indraAsLesmana/dl380-case/docs/02A_rail_final_upgrade.png

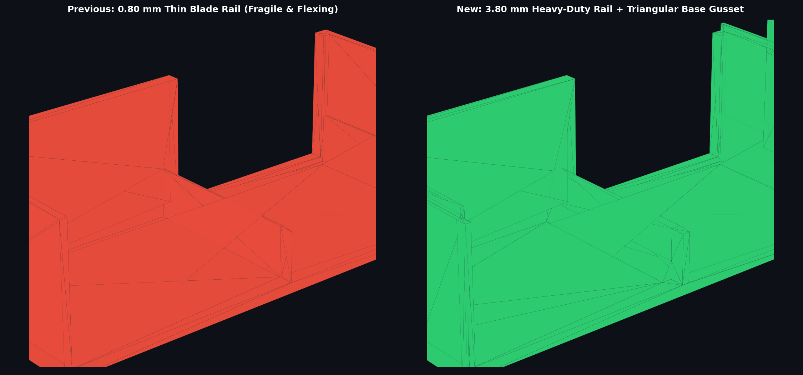
docs/02A_rail_final_upgrade.png
