indraAsLesmana/dl380-case/docs/02A_rail_thickness_comparison.png

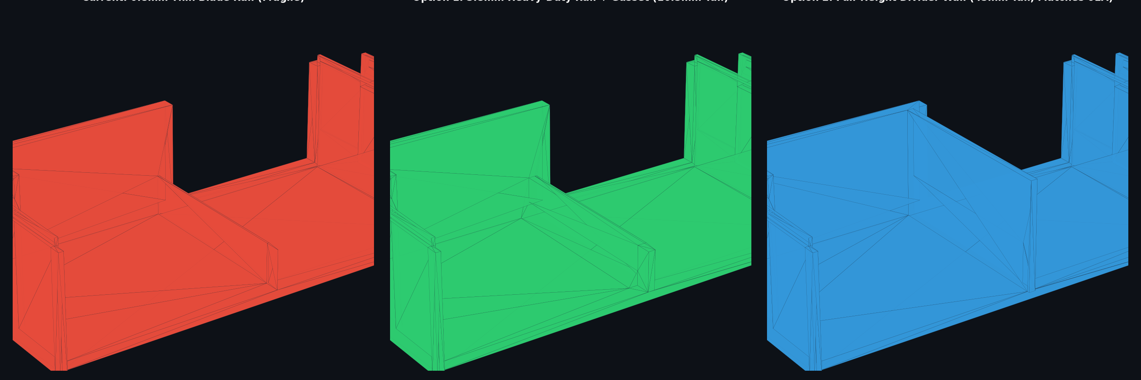
docs/02A_rail_thickness_comparison.png
