indraAsLesmana/dl380-case/docs/02A_rotation_warning.png

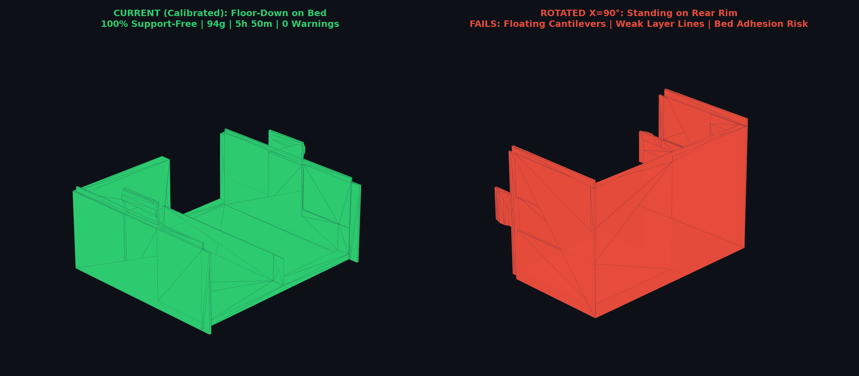
docs/02A_rotation_warning.png
