indraAsLesmana/dl380-case/docs/02A_snap_comparison.png

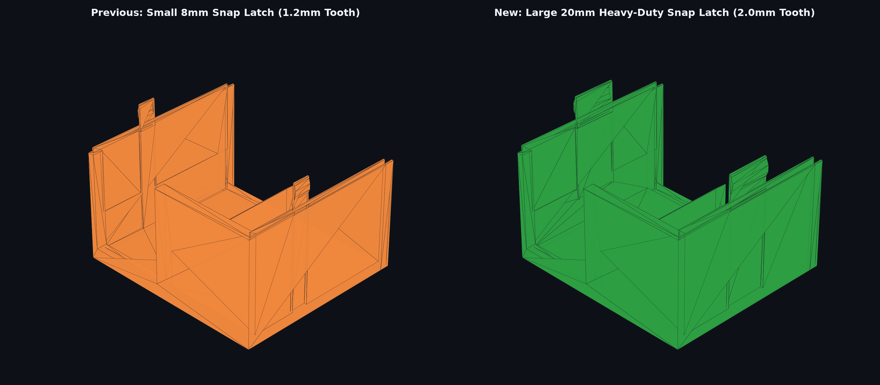
docs/02A_snap_comparison.png
