indraAsLesmana/dl380-case/docs/02A_snap_layer_diagram.png

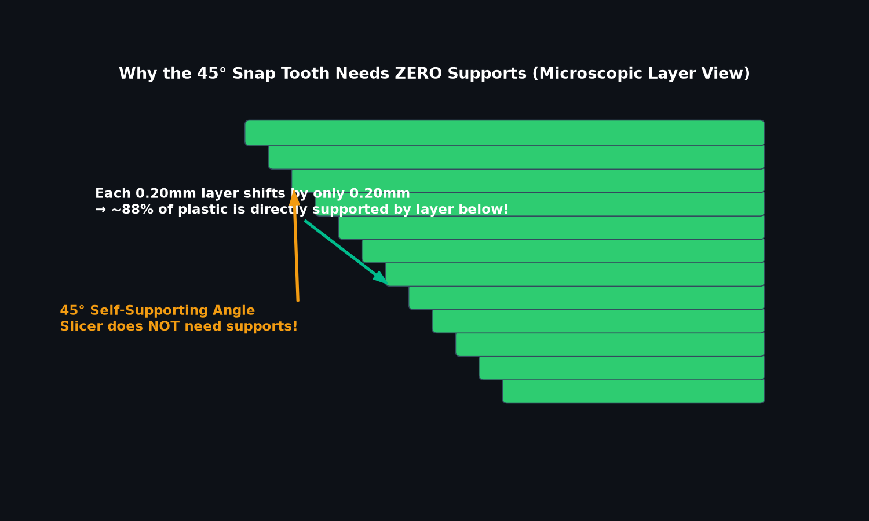
docs/02A_snap_layer_diagram.png
