indraAsLesmana/dl380-case/docs/02B_fan_grille_detail.png

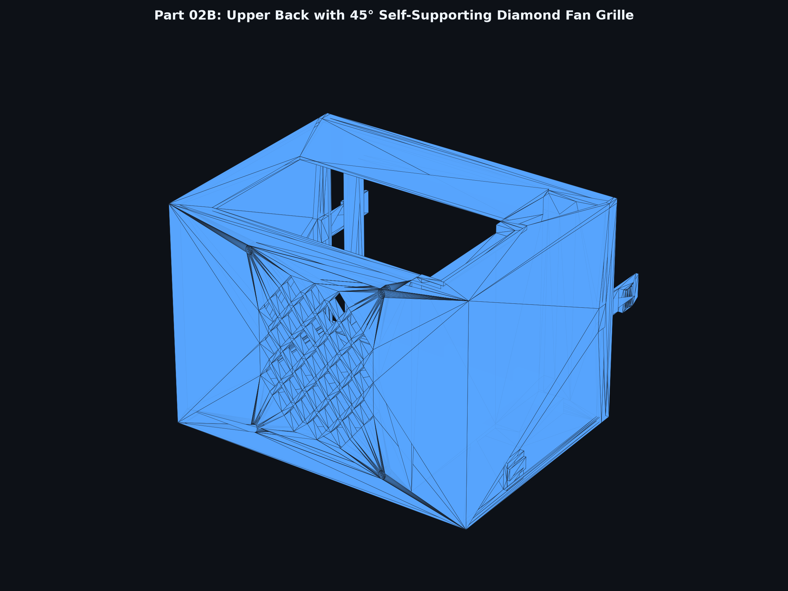
docs/02B_fan_grille_detail.png
