indraAsLesmana/dl380-case/docs/02B_thick_side_analysis.png

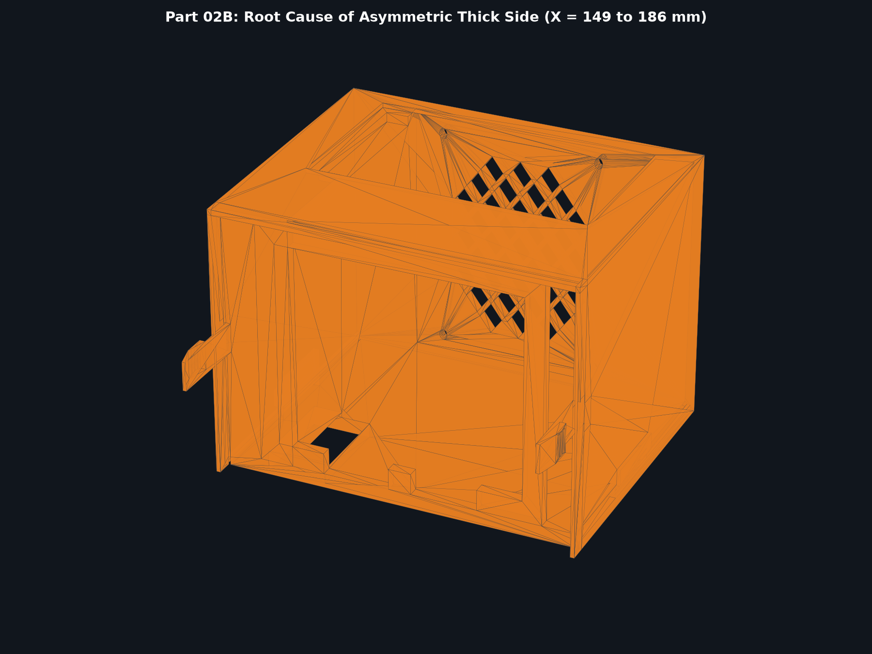
docs/02B_thick_side_analysis.png
