indraAsLesmana/dl380-case/docs/cage_retention_pin_diagram.png

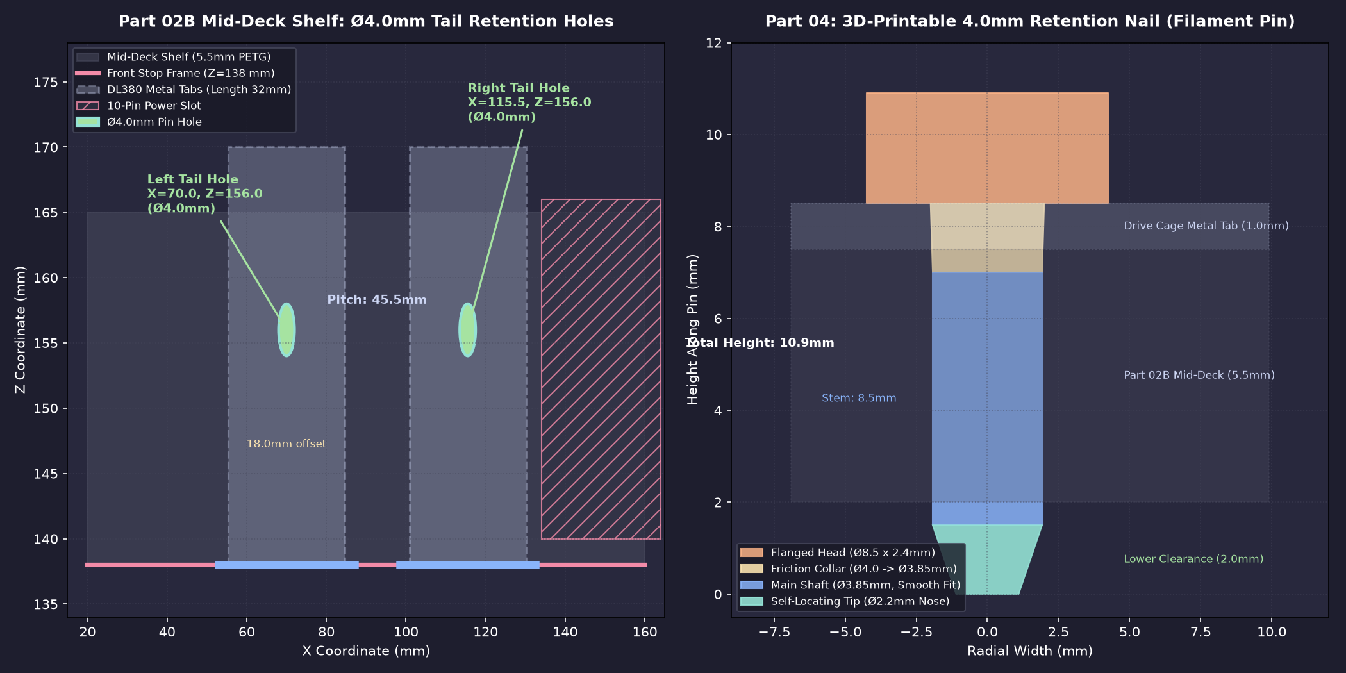
docs/cage_retention_pin_diagram.png
