indraAsLesmana/dl380-case/docs/digital_capler/10-pin-backplane-width.jpeg

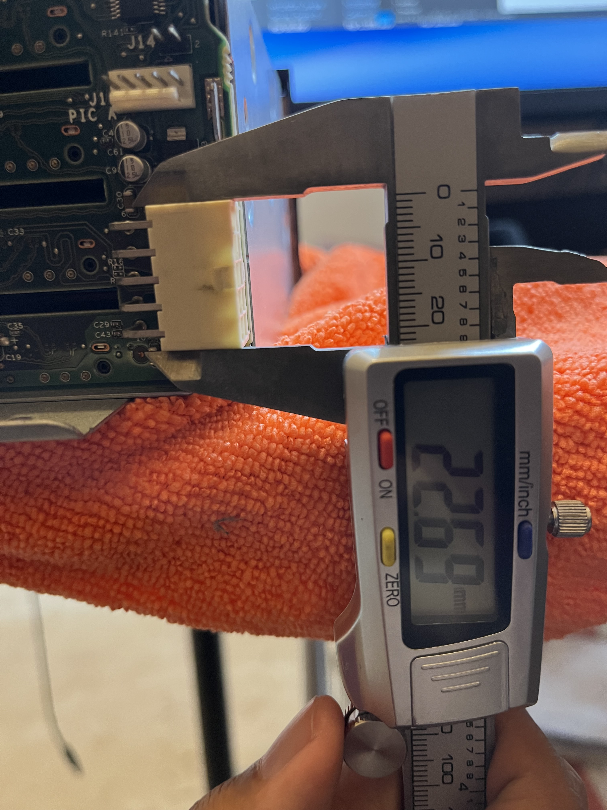
docs/digital_capler/10-pin-backplane-width.jpeg
