indraAsLesmana/dl380-case/docs/digital_capler/10-pin-to-top-backplane.jpeg

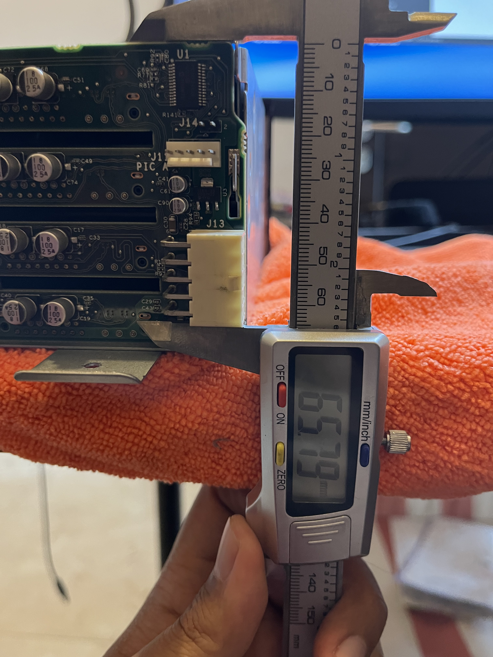
docs/digital_capler/10-pin-to-top-backplane.jpeg
