indraAsLesmana/dl380-case/docs/digital_capler/backplane_tail_height.jpeg

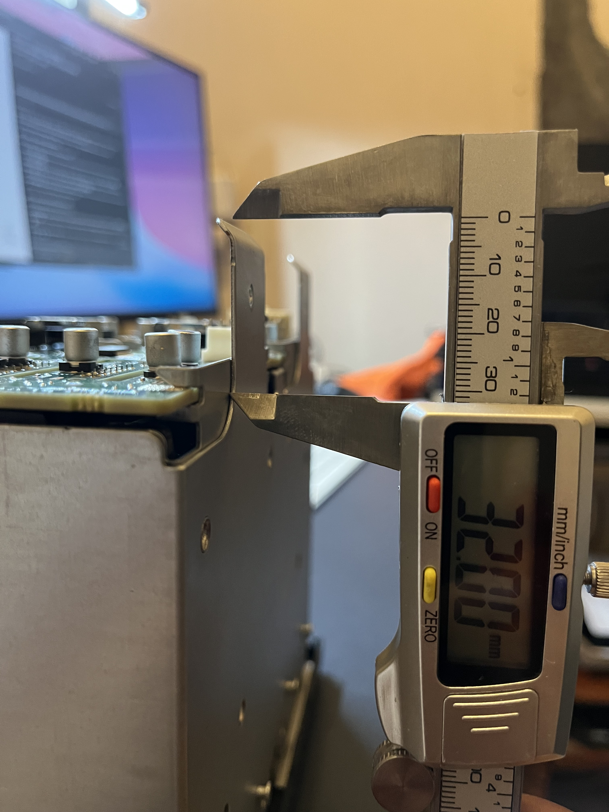
docs/digital_capler/backplane_tail_height.jpeg
