indraAsLesmana/dl380-case/docs/digital_capler/backplane_tail_width.jpeg

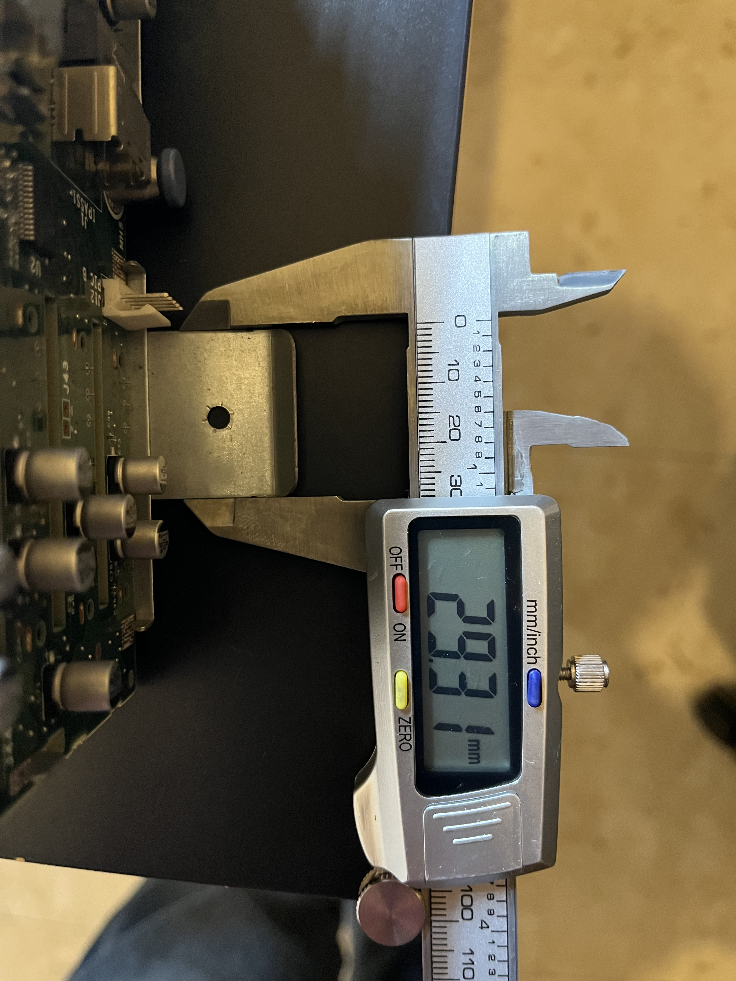
docs/digital_capler/backplane_tail_width.jpeg
