indraAsLesmana/dl380-case/docs/digital_capler/disc_cage_metal_height.jpeg

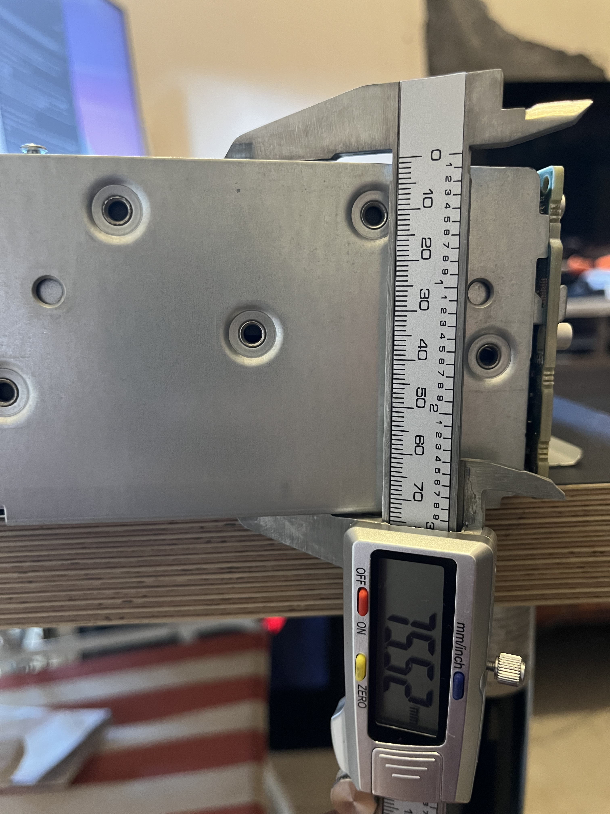
docs/digital_capler/disc_cage_metal_height.jpeg
