indraAsLesmana/dl380-case/docs/digital_capler/front_plastic_case_thick.jpeg

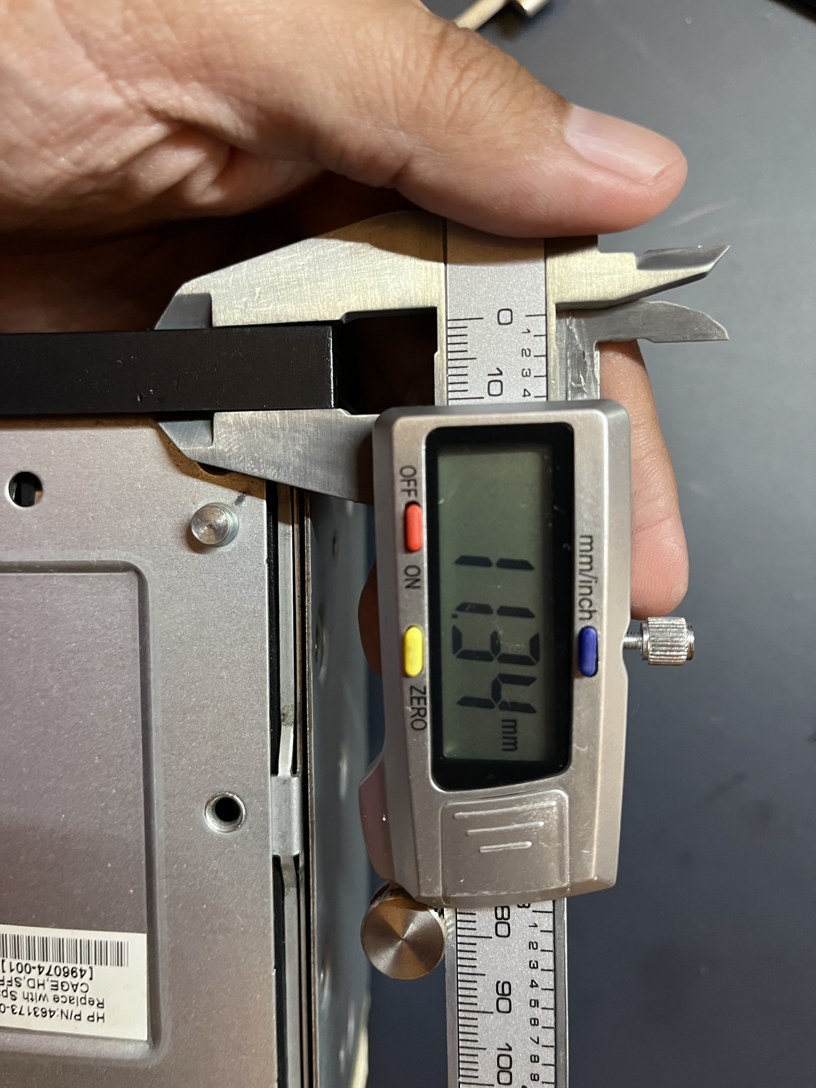
docs/digital_capler/front_plastic_case_thick.jpeg
