indraAsLesmana/dl380-case/docs/digital_capler/front_plastic_height.jpeg

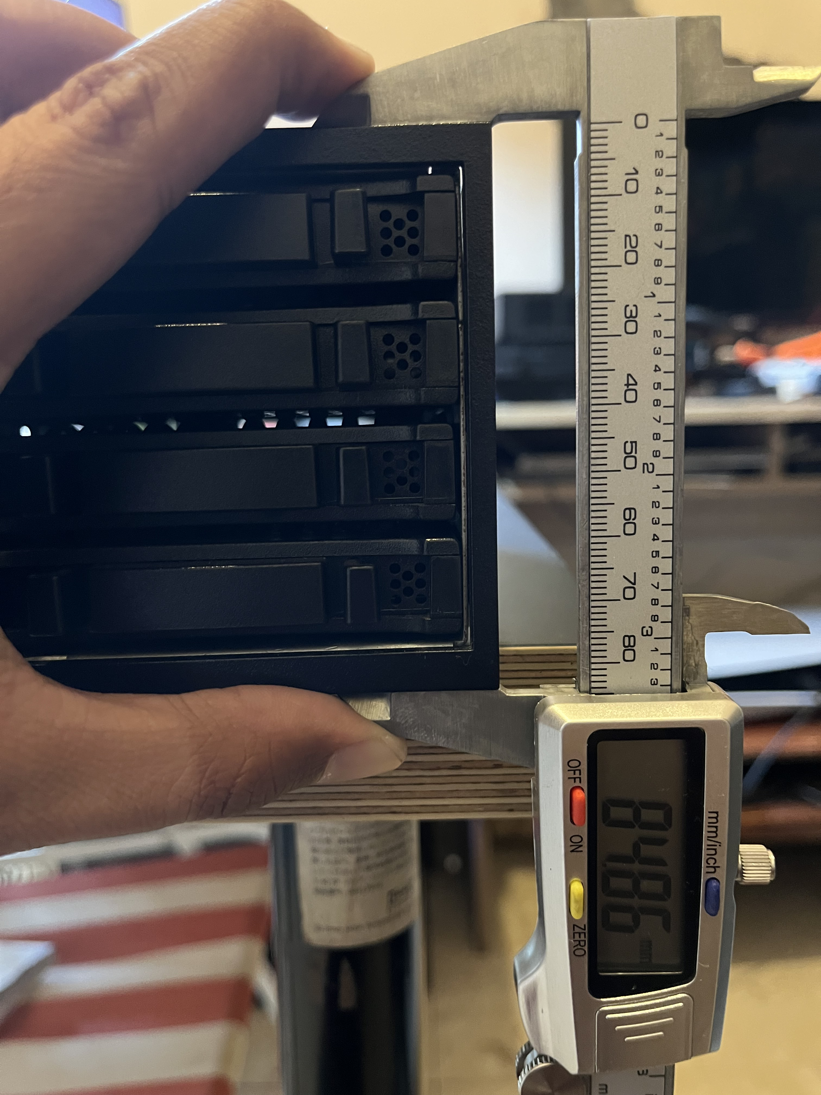
docs/digital_capler/front_plastic_height.jpeg
