indraAsLesmana/dl380-case/docs/digital_capler/top_disccage_to_plastic_front_bottom-height.jpeg

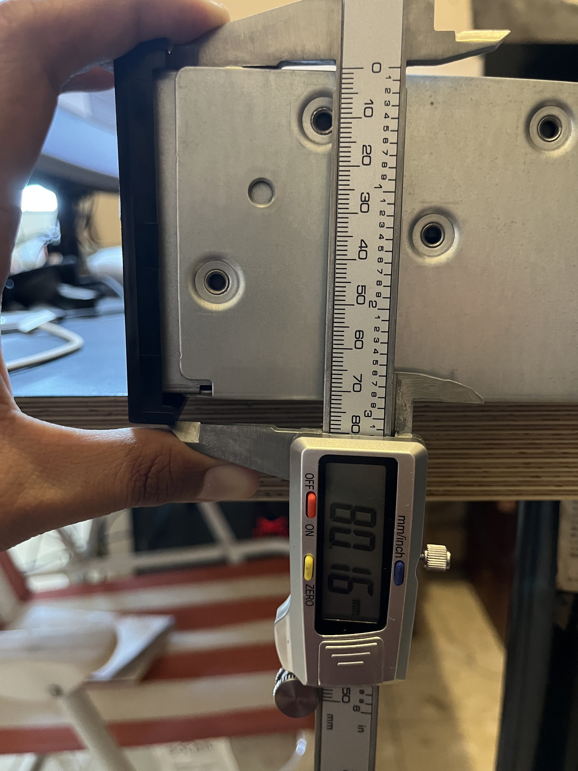
docs/digital_capler/top_disccage_to_plastic_front_bottom-height.jpeg
