indraAsLesmana/dl380-case/docs/dl380_flex_case_views.png

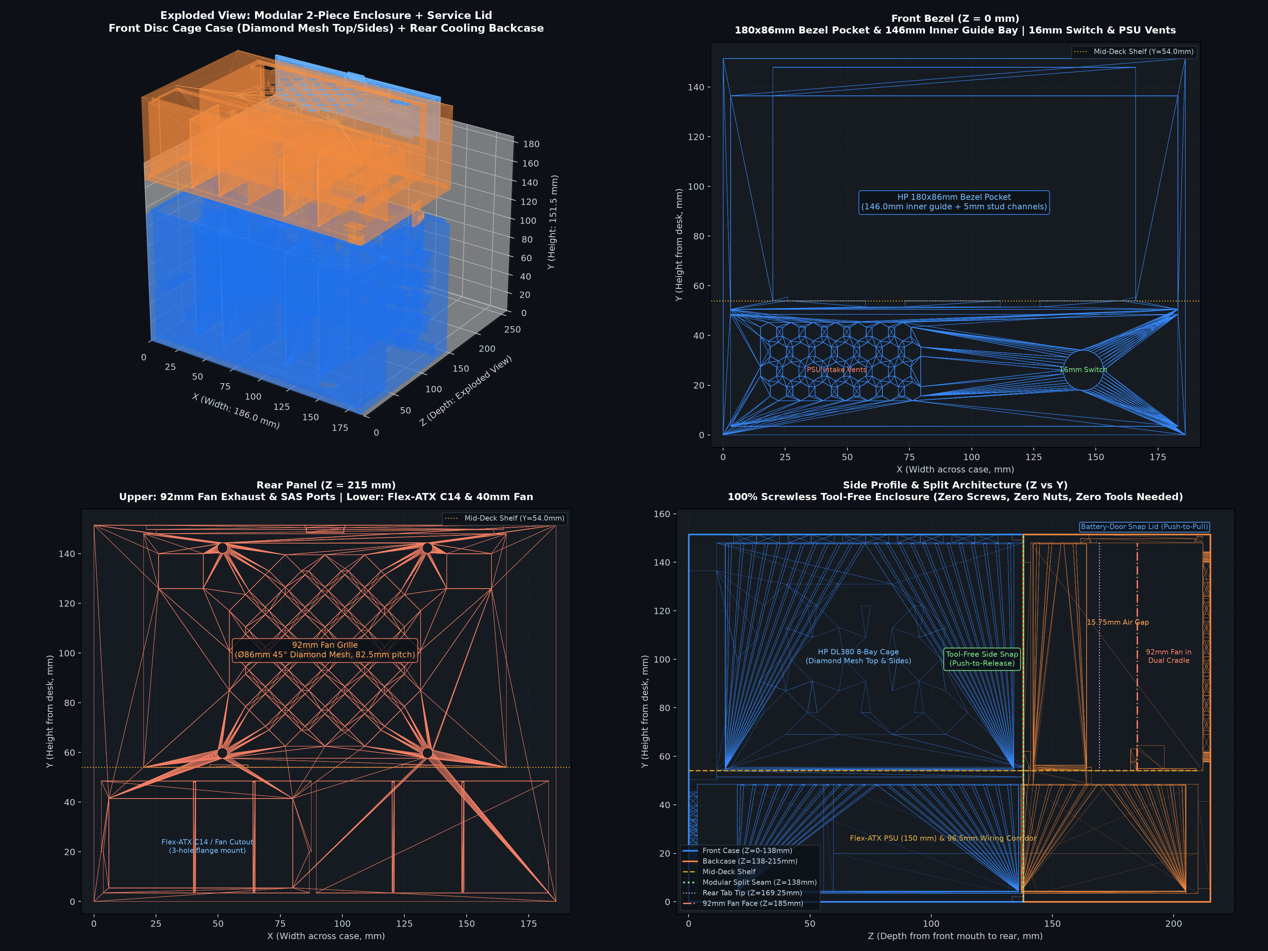
docs/dl380_flex_case_views.png
