indraAsLesmana/dl380-case/docs/fan_grille_comparison.png

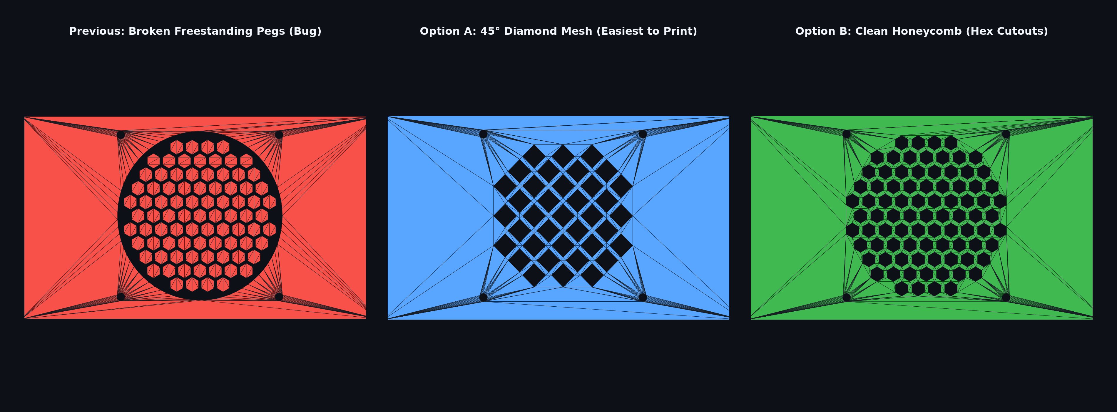
docs/fan_grille_comparison.png
