indraAsLesmana/dl380-case/docs/orientation_analysis_comparison.png

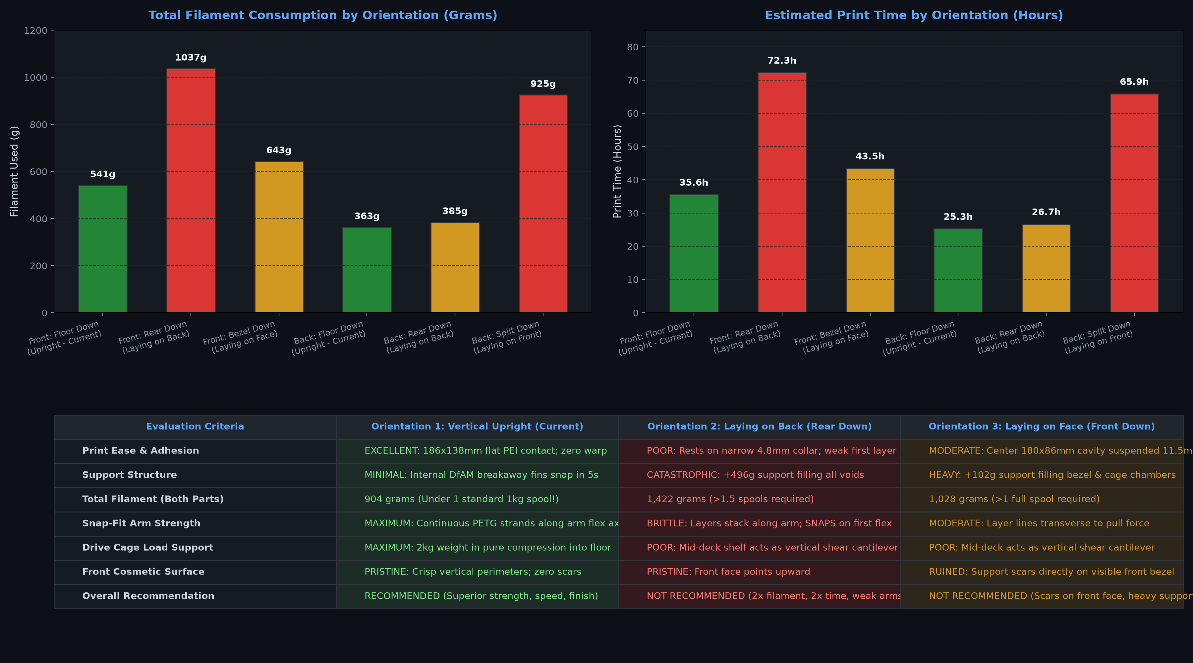
docs/orientation_analysis_comparison.png
