indraAsLesmana/dl380-case/docs/psu_tool_free_retention.png

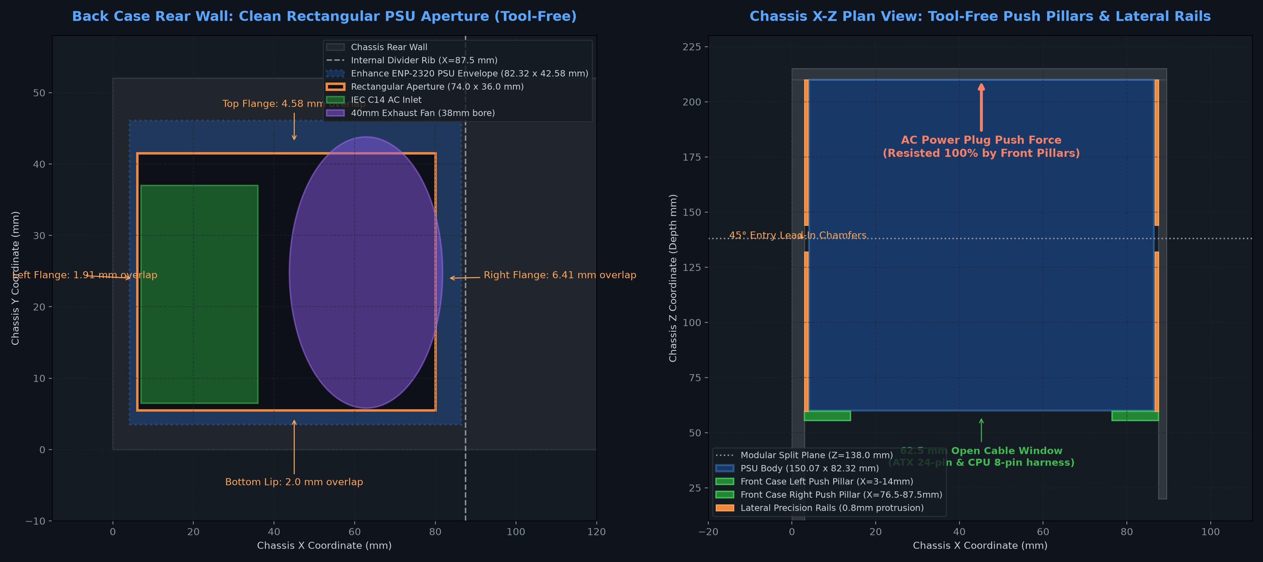
docs/psu_tool_free_retention.png
