indraAsLesmana/dl380-case/docs/reference/cage-rear-upright-cable.png

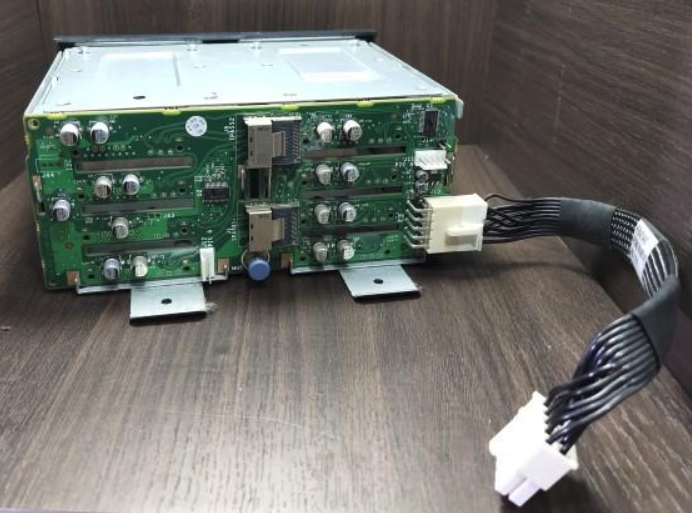
docs/reference/cage-rear-upright-cable.png
