indraAsLesmana/dl380-case/docs/reference/psu-dimension/IMG_1393.jpeg

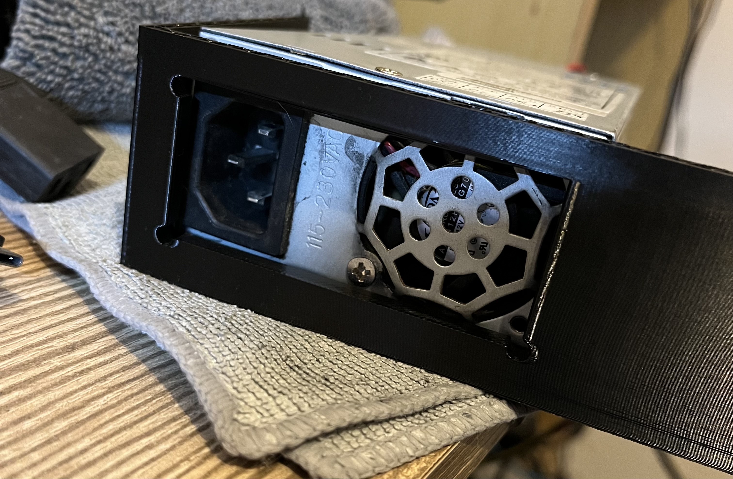
docs/reference/psu-dimension/IMG_1393.jpeg
