indraAsLesmana/dl380-case/docs/reference/s-l1600 front.webp

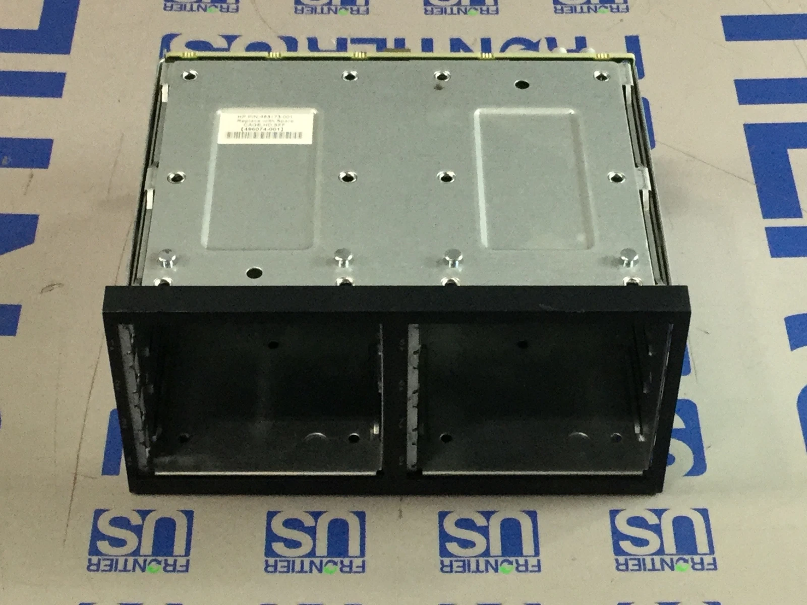
docs/reference/s-l1600 front.webp
