indraAsLesmana/dl380-case/out/body_side.png

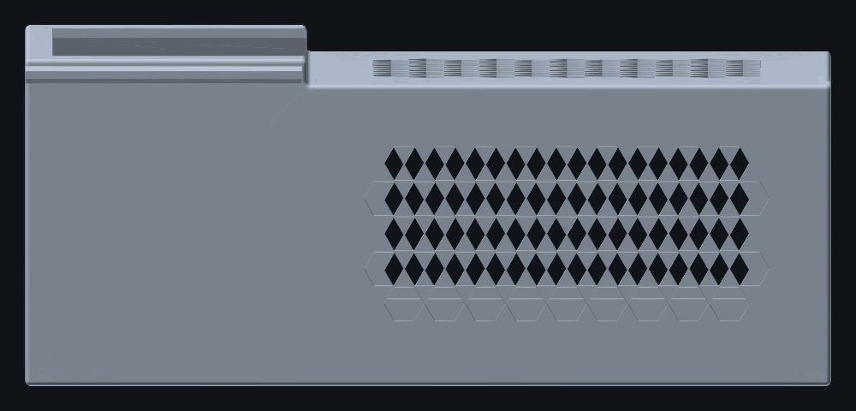
out/body_side.png
