indraAsLesmana/dl380-case/out/body_top.png

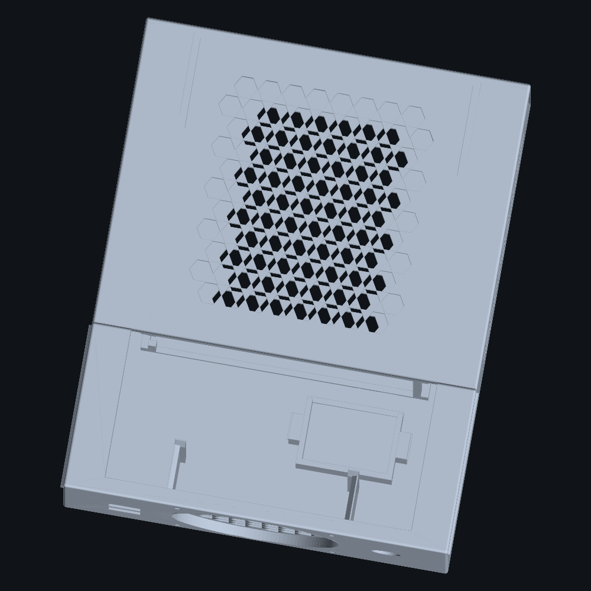
out/body_top.png
