indraAsLesmana/dl380-case/out/lid_cut.png

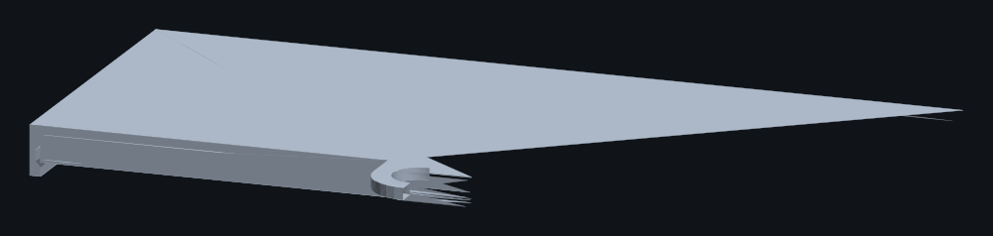
out/lid_cut.png
