indraAsLesmana/dl380-case/out/lid_front.png

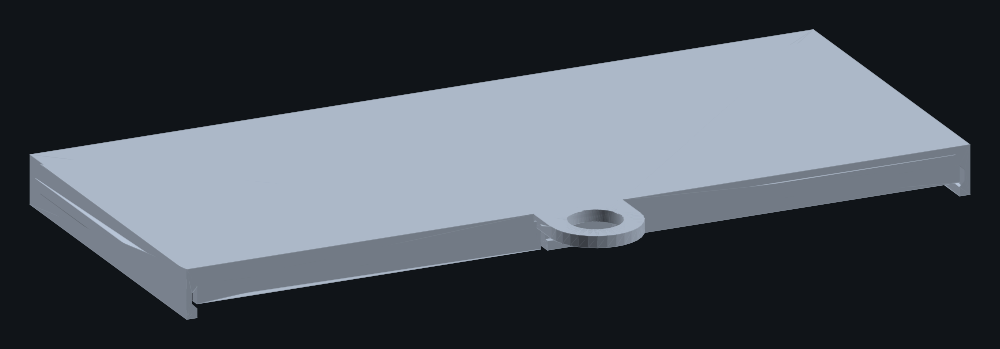
out/lid_front.png
