indraAsLesmana/dl380-case/out/lid_rear.png

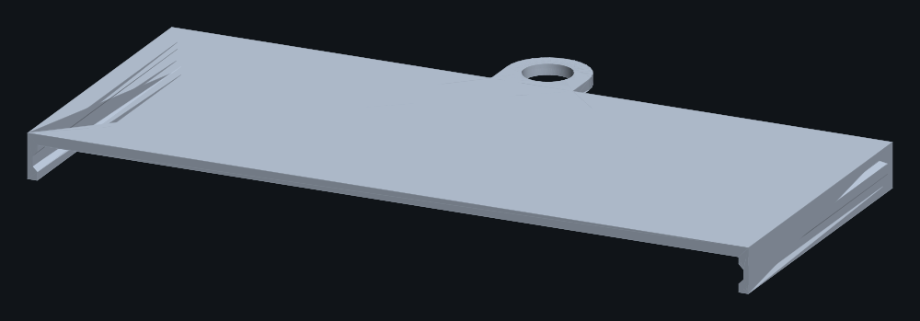
out/lid_rear.png
