indraAsLesmana/dl380-case/out/lid_side.png

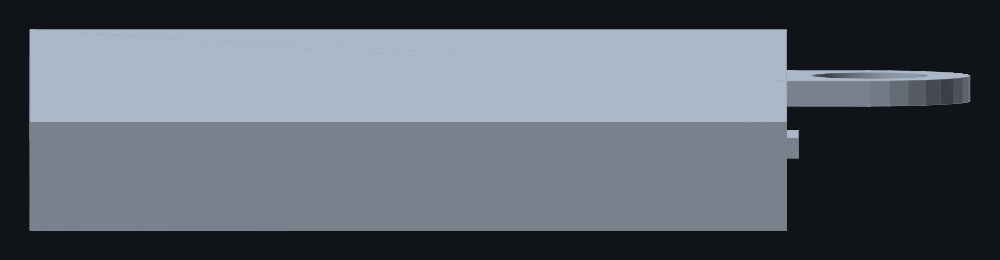
out/lid_side.png
