indraAsLesmana/dl380-case/out/lid_top.png

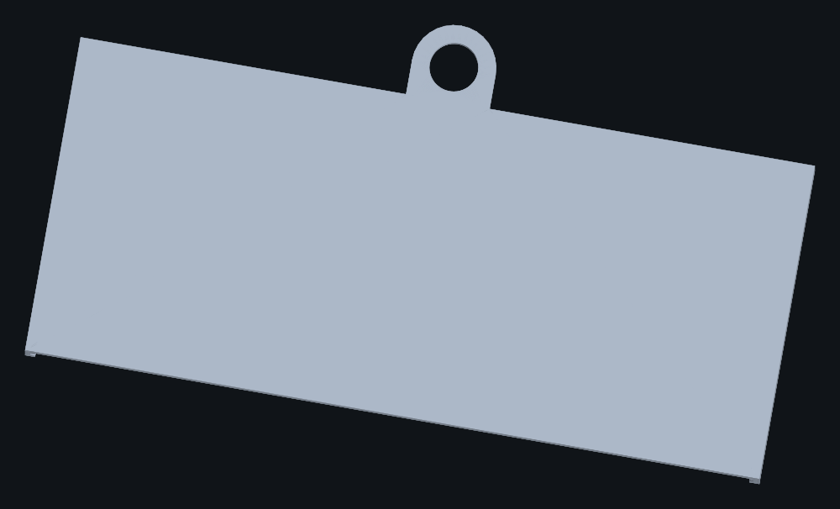
out/lid_top.png
