indraAsLesmana/dl380-case/out/strap_cut.png

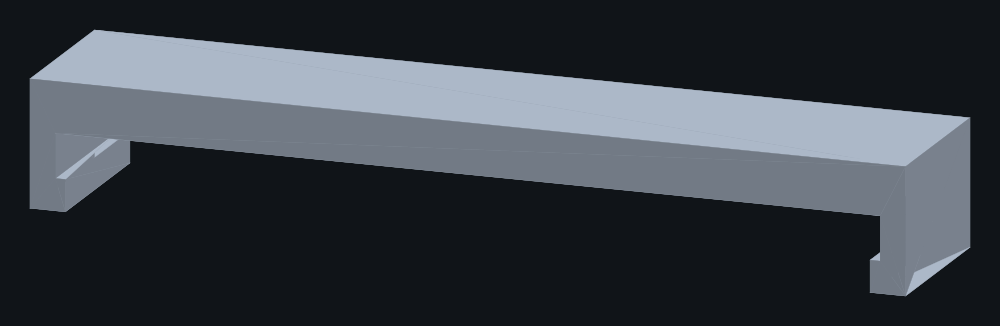
out/strap_cut.png
