indraAsLesmana/dl380-case/out/strap_front.png

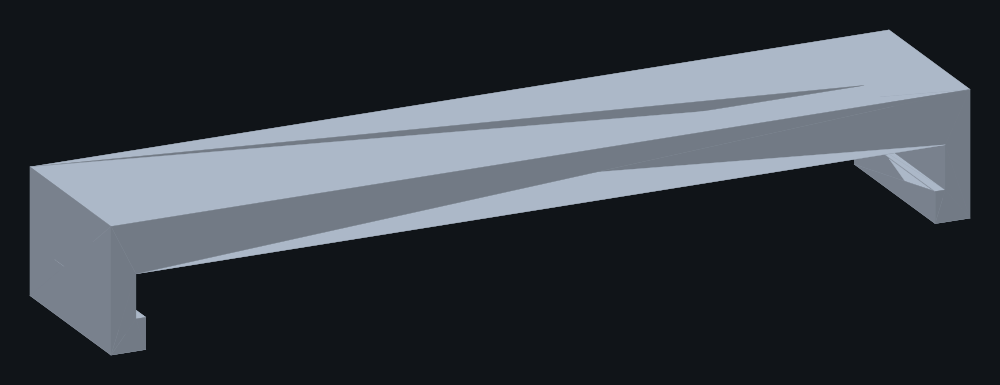
out/strap_front.png
