indraAsLesmana/dl380-case/out/strap_top.png

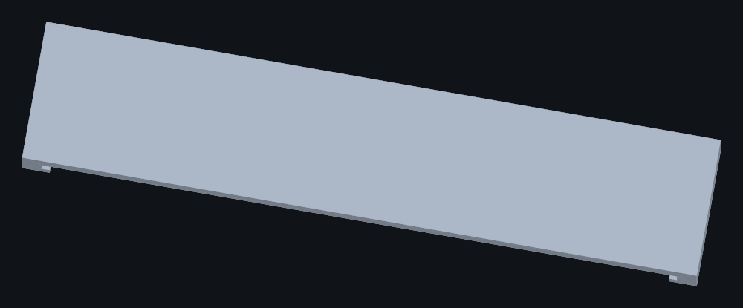
out/strap_top.png
