indraAsLesmana/dl380-case/print/dl380_back_case.stl

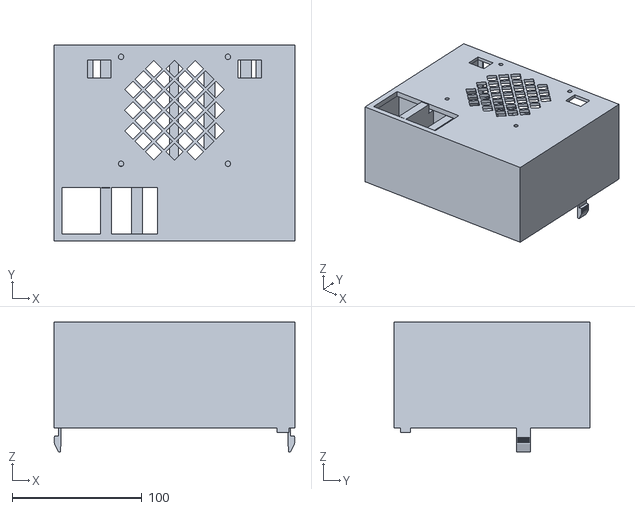
[picture p64: CAD file, 2026-10-03]
print/dl380_back_case.stl
186.0 x 151.5 x 100.0
