indraAsLesmana/dl380-case/out/4piece/01B_upper_front.step

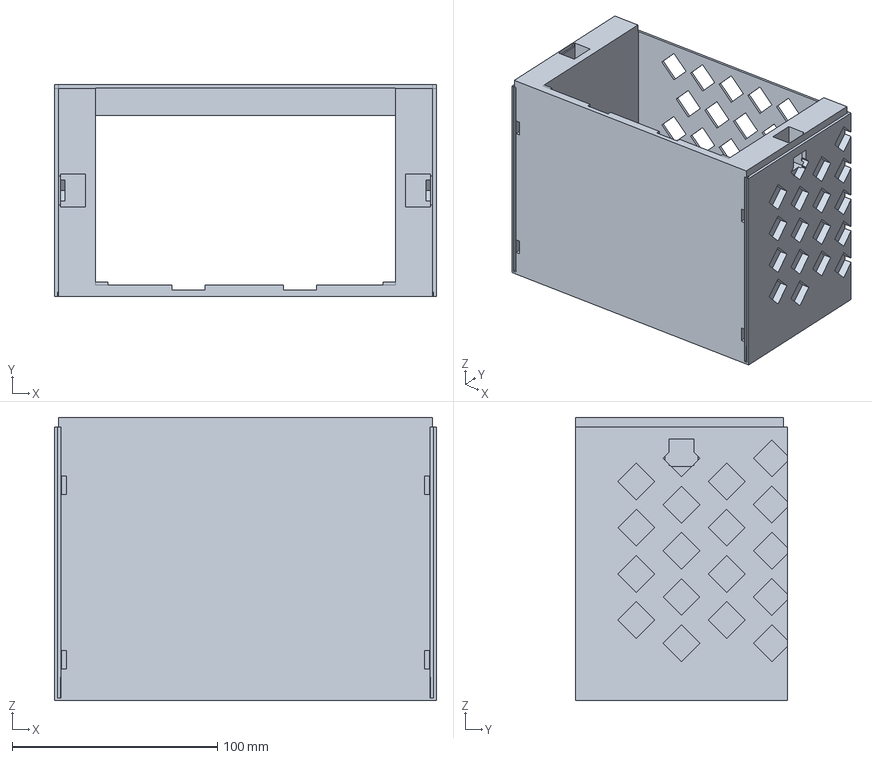
[picture p65: CAD file, 2026-10-03]
out/4piece/01B_upper_front.step
186.0 x 103.0 x 138.0 mm
