indraAsLesmana/dl380-case/out/4piece/04_drive_cage_pin.step

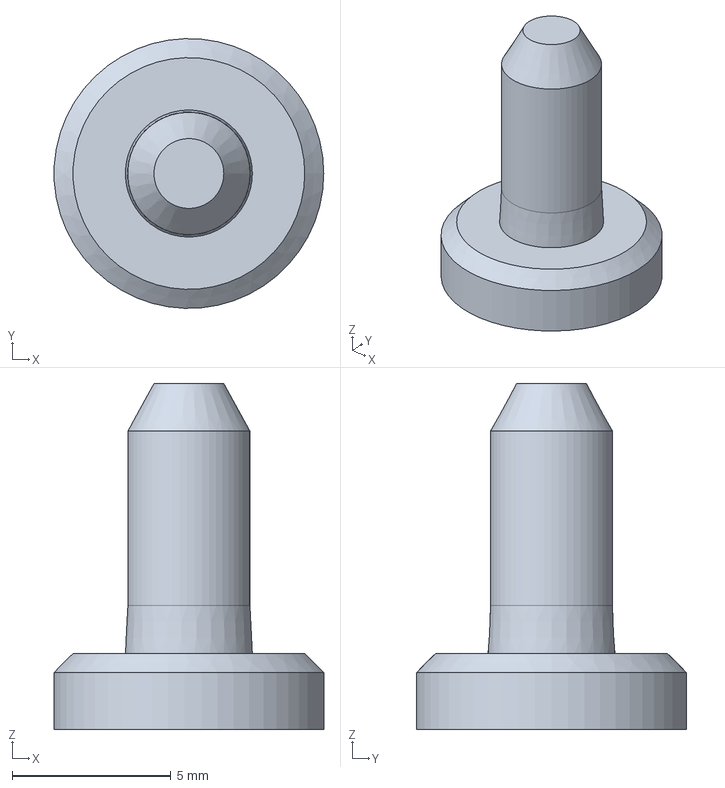
[picture p66: CAD file, 2026-10-03]
out/4piece/04_drive_cage_pin.step
8.49 x 8.50 x 10.9 mm
