indraAsLesmana/dl380-case/print_service_package/4piece/03_dl380_service_lid.3mf

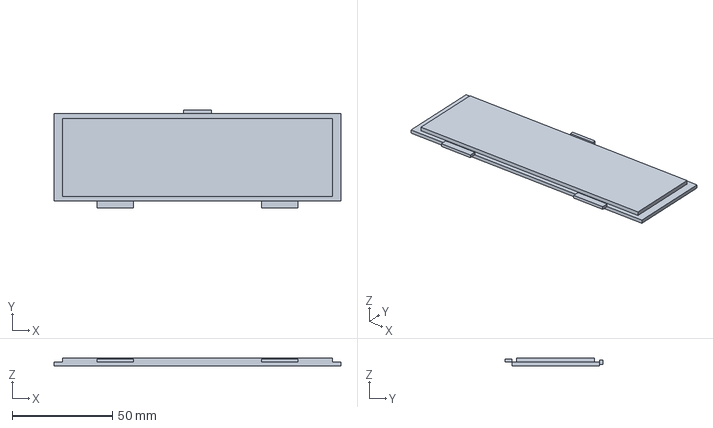
[picture p67: CAD file, 2026-10-03]
print_service_package/4piece/03_dl380_service_lid.3mf
143.0 x 49.0 x 3.80 mm
