indraAsLesmana/dl380-case/out/dl380_flex_case.step

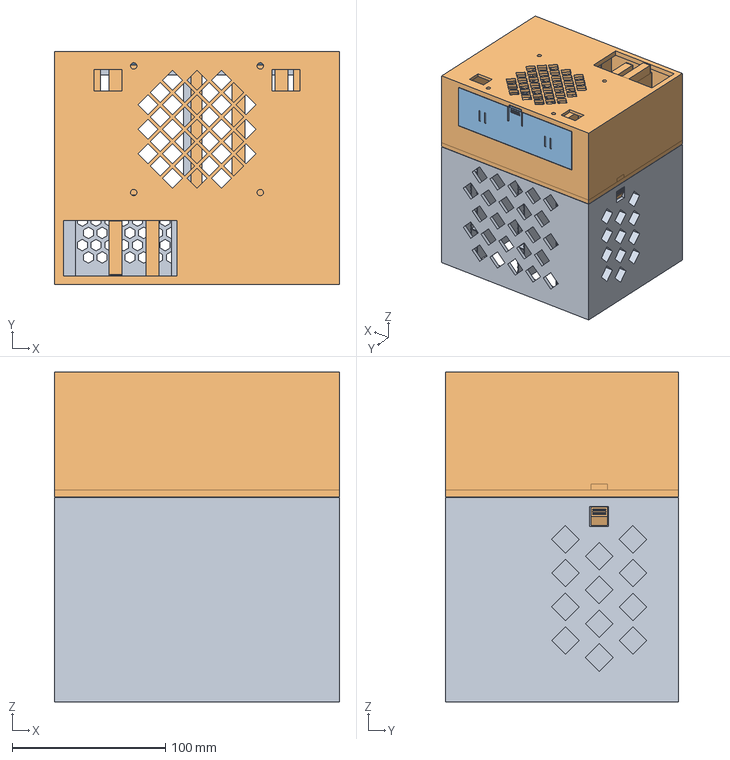
[picture p68: CAD file, 2026-10-03]
out/dl380_flex_case.step
186.0 x 151.5 x 215.0 mm
