indraAsLesmana/dl380-case/print/dl380_flex_case_all-parts.stl

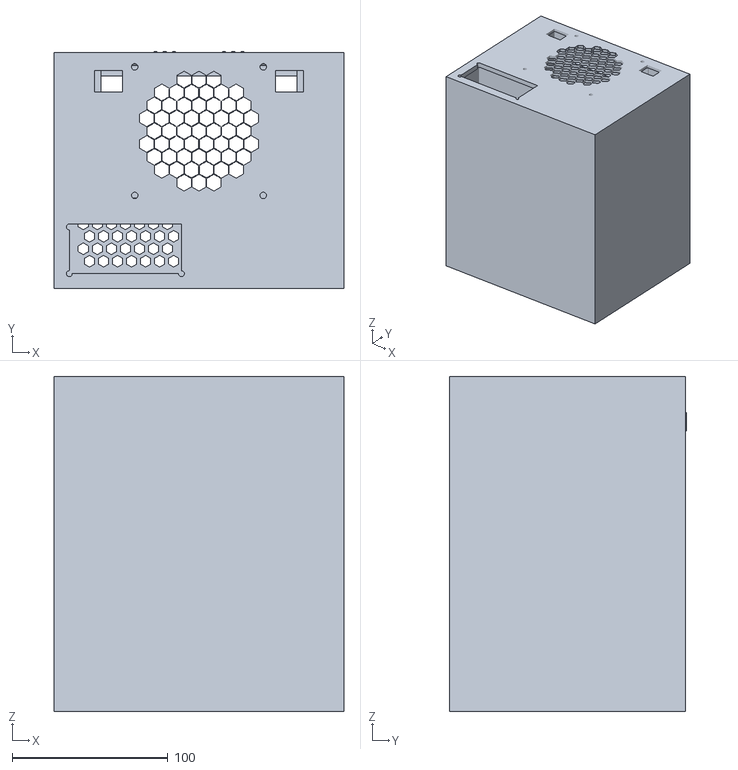
[picture p69: CAD file, 2026-09-29]
print/dl380_flex_case_all-parts.stl
186.0 x 152.1 x 215.0
