indraAsLesmana/dl380-case/print/dl380-case_psu-strap.stl

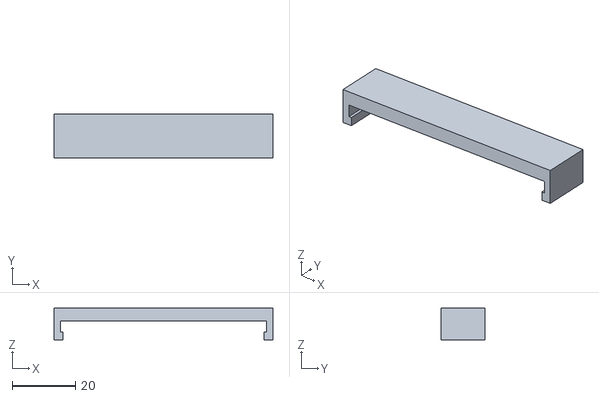
[picture p70: CAD file, 2026-09-24]
print/dl380-case_psu-strap.stl
69.2 x 14.0 x 10.0
