indraAsLesmana/dl380-case/out/dl380_flex_case_lid.step

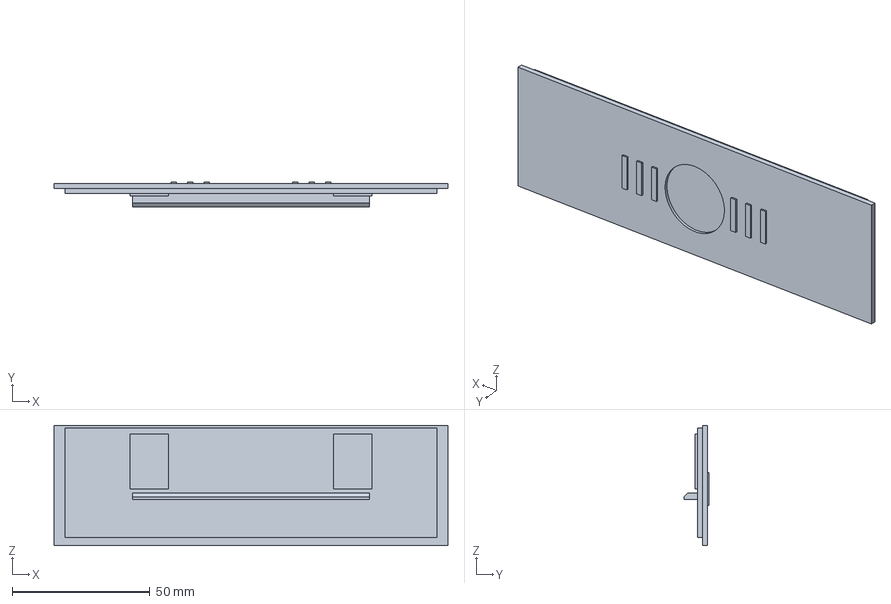
[picture p71: CAD file, 2026-09-29]
out/dl380_flex_case_lid.step
143.0 x 9.10 x 43.7 mm
