indraAsLesmana/dl380-case/print/dl380-case_body.stl

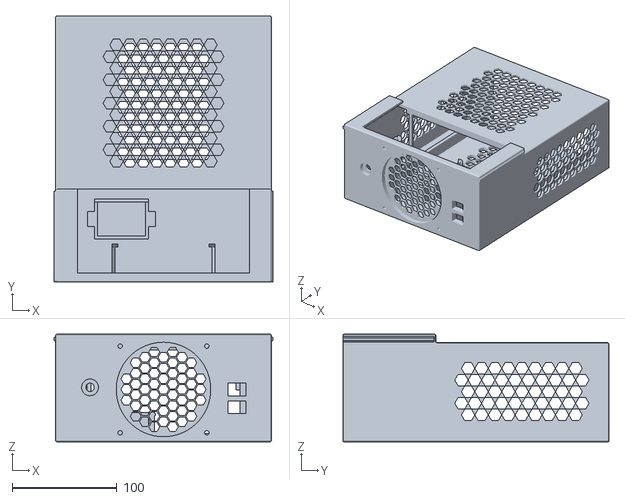
[picture p72: CAD file, 2026-09-24]
print/dl380-case_body.stl
208.4 x 253.4 x 102.8
