indraAsLesmana/dl380-case/print_service_package/4piece/04_dl380_cage_pins.3mf

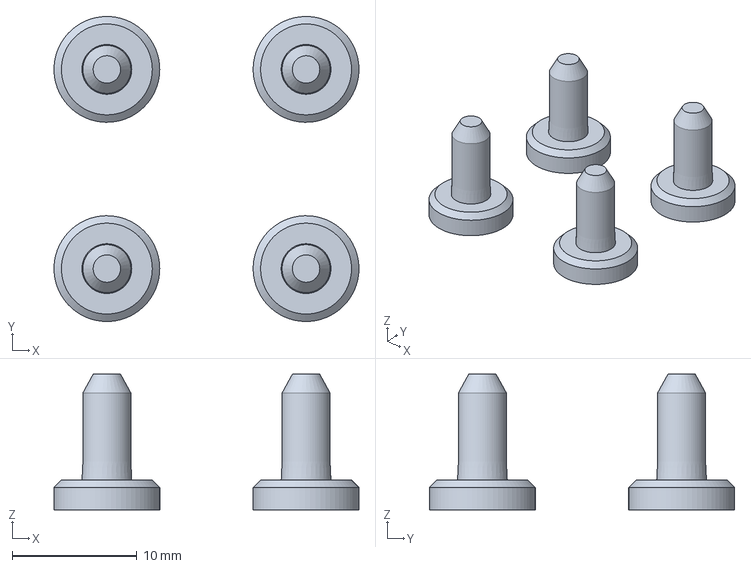
[picture p73: CAD file, 2026-10-03]
print_service_package/4piece/04_dl380_cage_pins.3mf
24.5 x 24.5 x 10.9 mm
