indraAsLesmana/dl380-case/out/dl380_flex_case_body.step

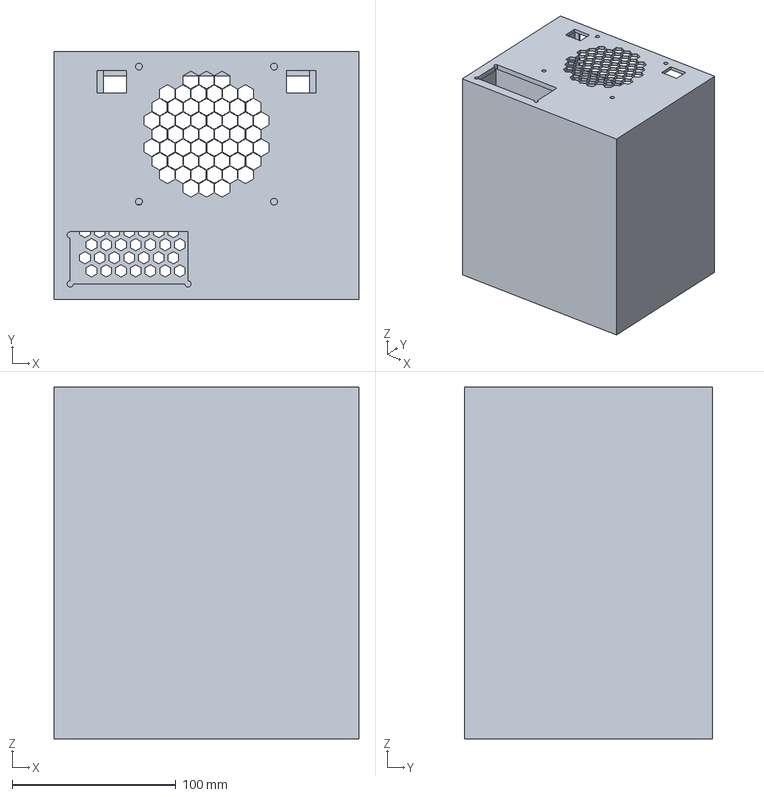
[picture p74: CAD file, 2026-09-29]
out/dl380_flex_case_body.step
186.0 x 151.5 x 215.0 mm
