indraAsLesmana/dl380-case/print/dl380-case_all-parts.stl

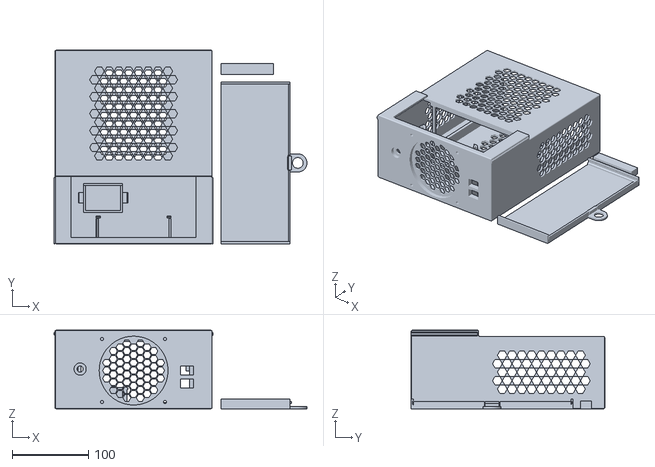
[picture p75: CAD file, 2026-09-24]
print/dl380-case_all-parts.stl
331.2 x 253.4 x 102.8
