indraAsLesmana/dl380-case/out/dl380_cage_case_lid.step

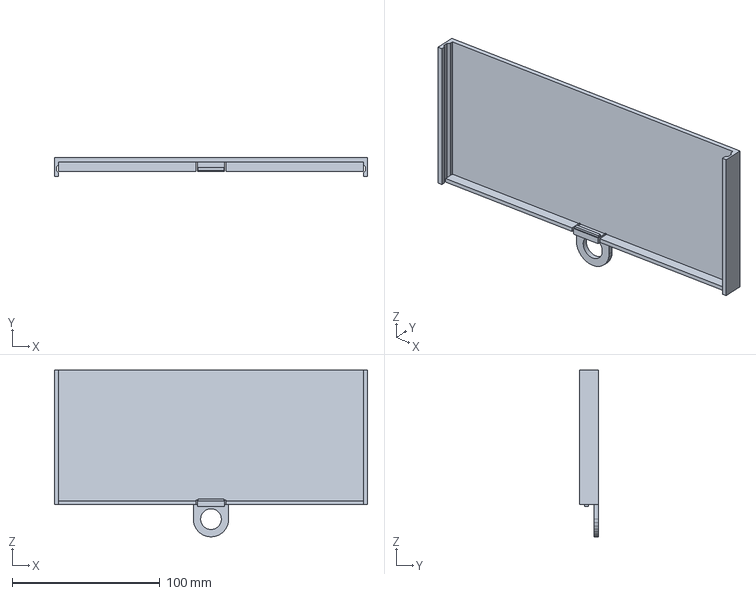
[picture p76: CAD file, 2026-09-24]
out/dl380_cage_case_lid.step
211.7 x 13.0 x 112.8 mm
