indraAsLesmana/dl380-case/out/dl380_cage_case.step

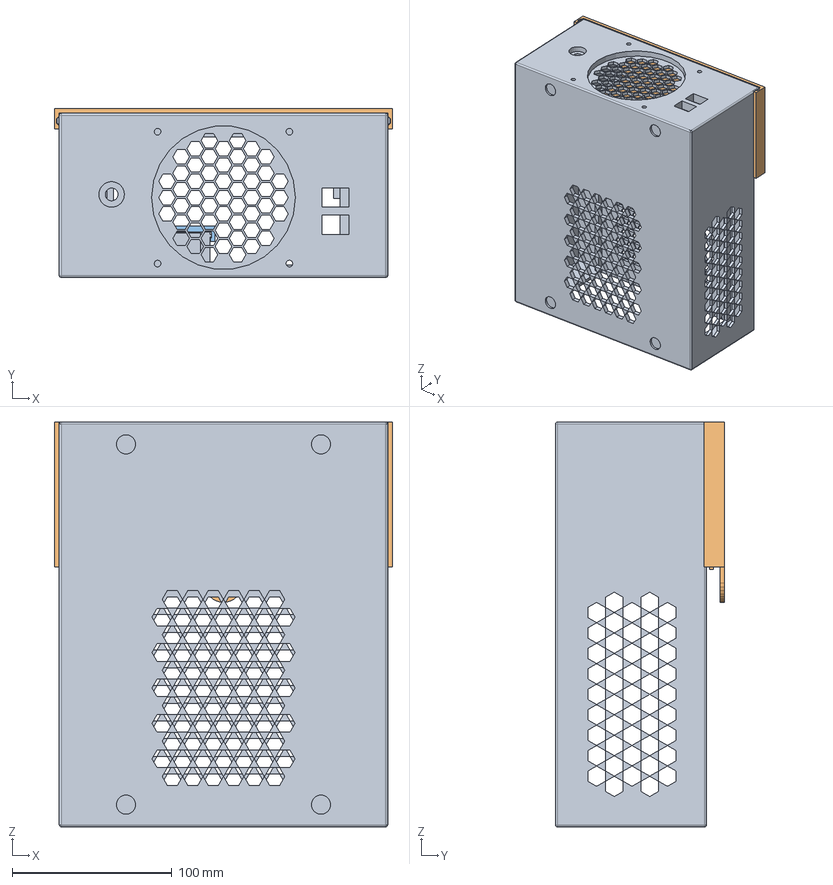
[picture p77: CAD file, 2026-09-24]
out/dl380_cage_case.step
211.7 x 105.8 x 253.4 mm
Case_Body
Service_Lid
PicoPSU_Strap
