indraAsLesmana/dl380-case/print_service_package/psu_center_support_view.png

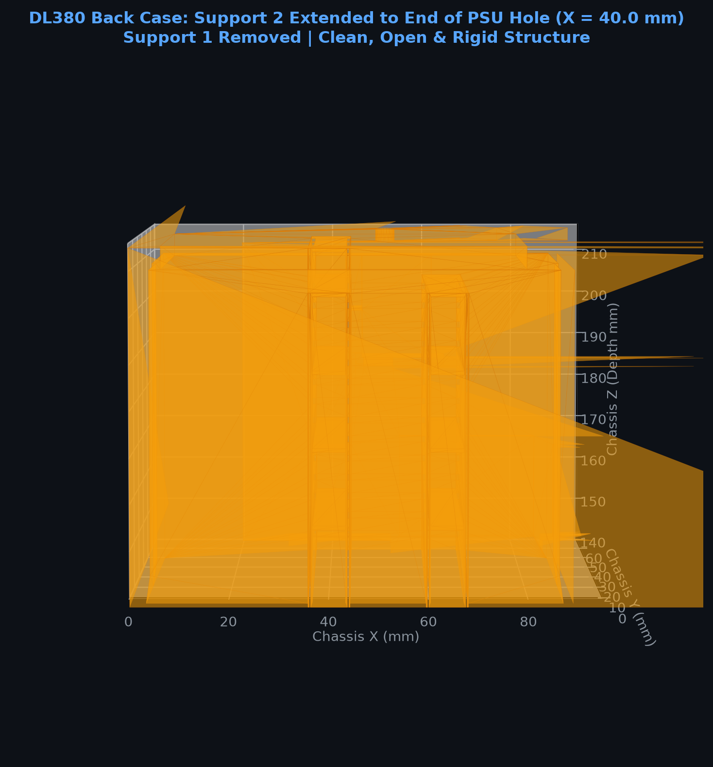
print_service_package/psu_center_support_view.png
