indraAsLesmana/dl380-case/docs/psu_clearance_verification.png

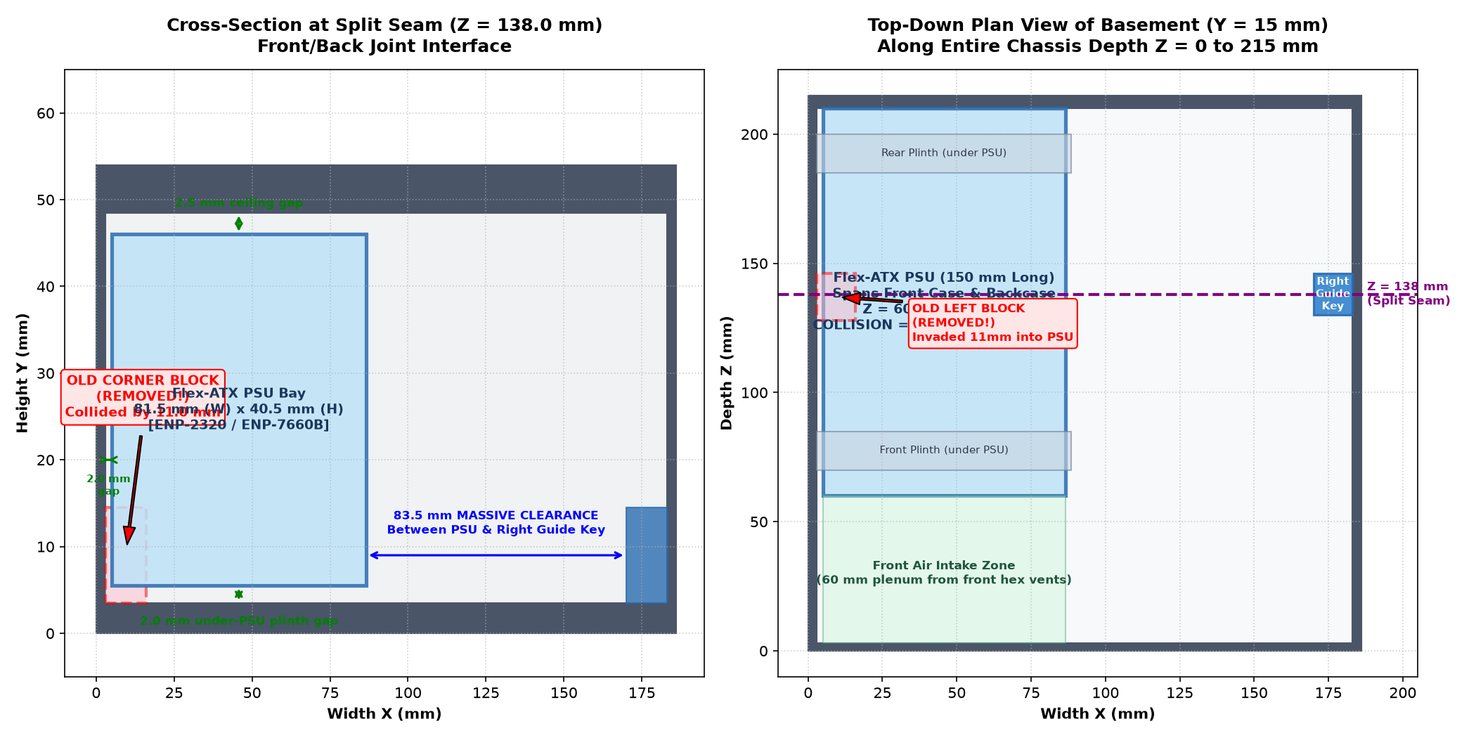
docs/psu_clearance_verification.png
