indraAsLesmana/dl380-case/docs/reference/psu-dimension/psu_rear_wall_calibrated.png

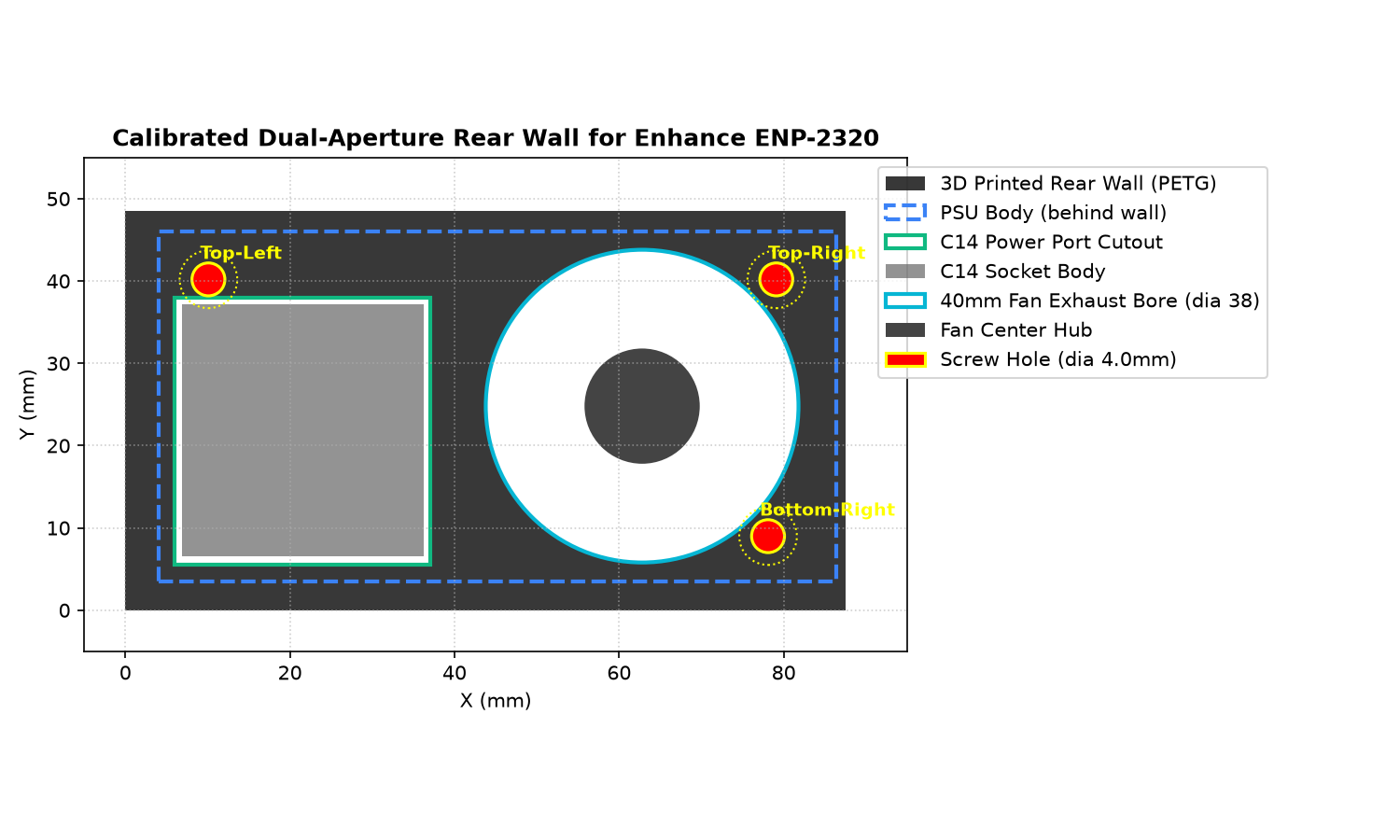
docs/reference/psu-dimension/psu_rear_wall_calibrated.png
