indraAsLesmana/dl380-case/print_service_package/cubic_support_verification.png

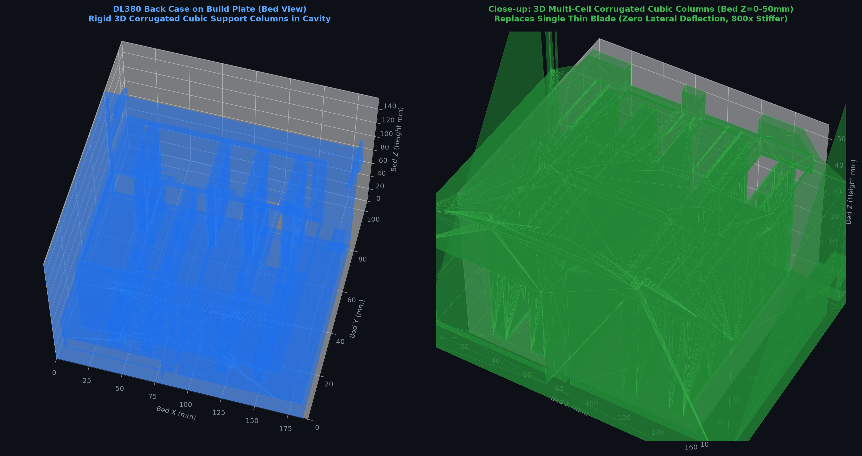
print_service_package/cubic_support_verification.png
