indraAsLesmana/dl380-case/docs/digital_capler/bottom-mosrom-center.jpeg

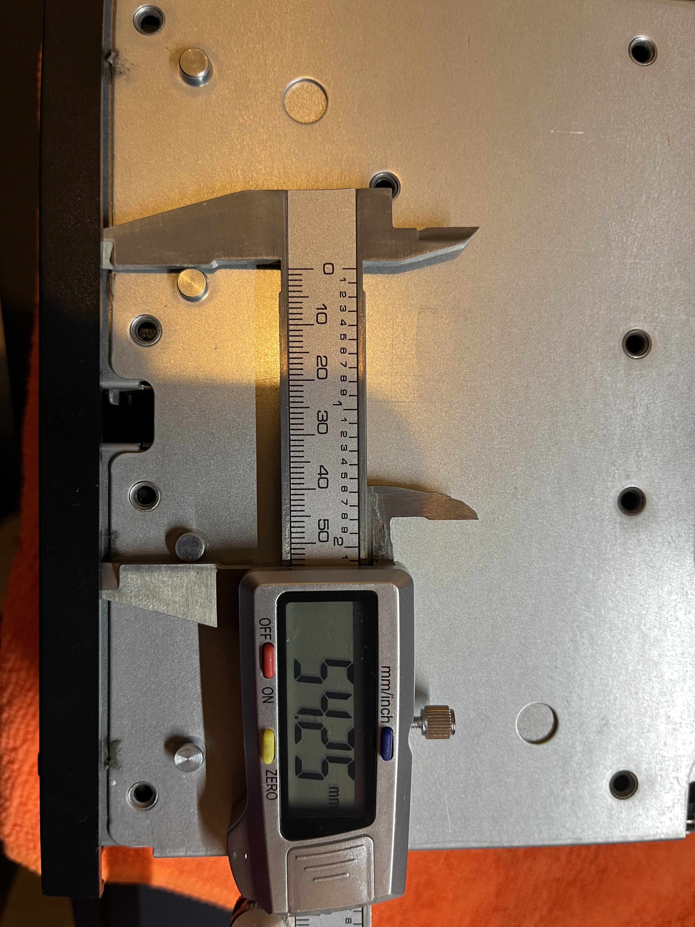
docs/digital_capler/bottom-mosrom-center.jpeg
