indraAsLesmana/dl380-case/docs/digital_capler/bottom-mosrom-left.jpeg

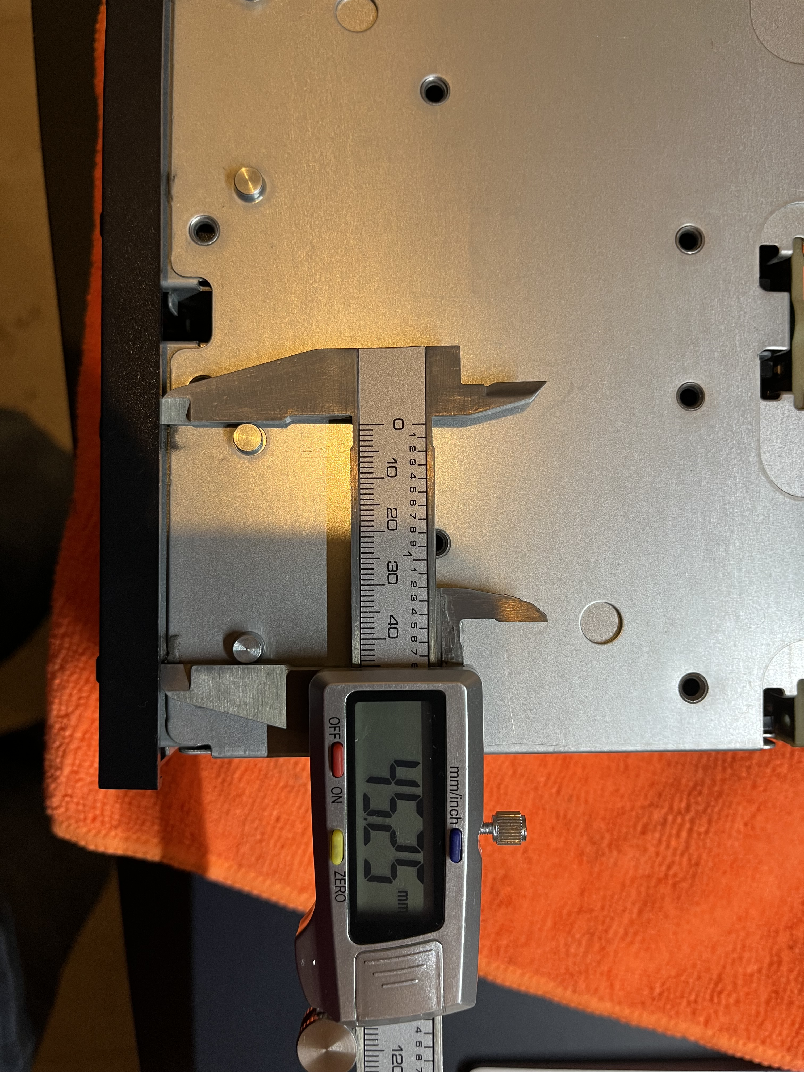
docs/digital_capler/bottom-mosrom-left.jpeg
