indraAsLesmana/dl380-case/docs/digital_capler/top-moshrom-right.jpeg

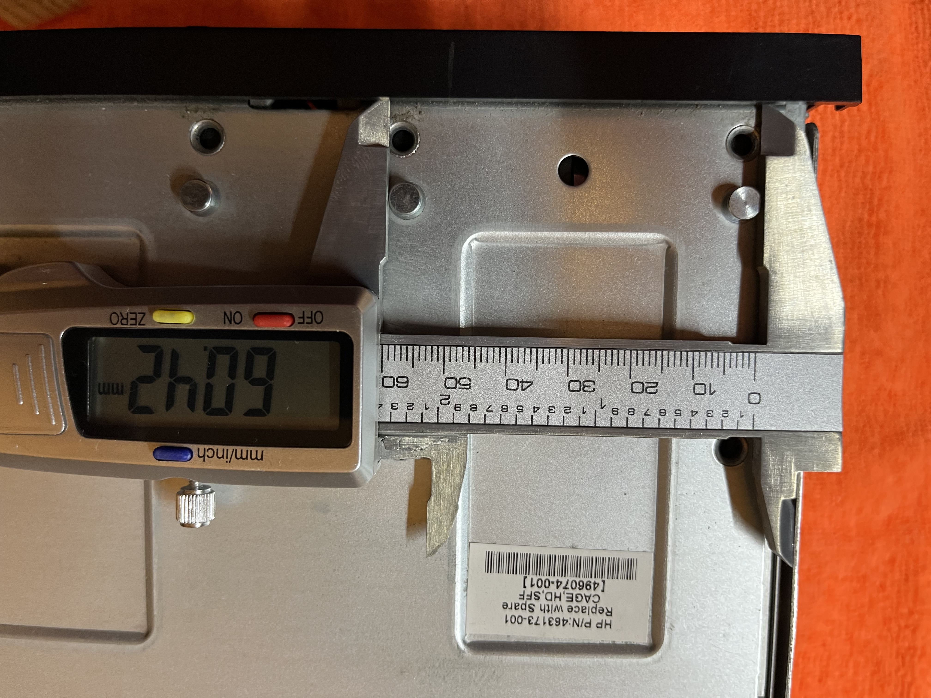
docs/digital_capler/top-moshrom-right.jpeg
