indraAsLesmana/dl380-case/docs/digital_capler/top-mosrom-left.jpeg

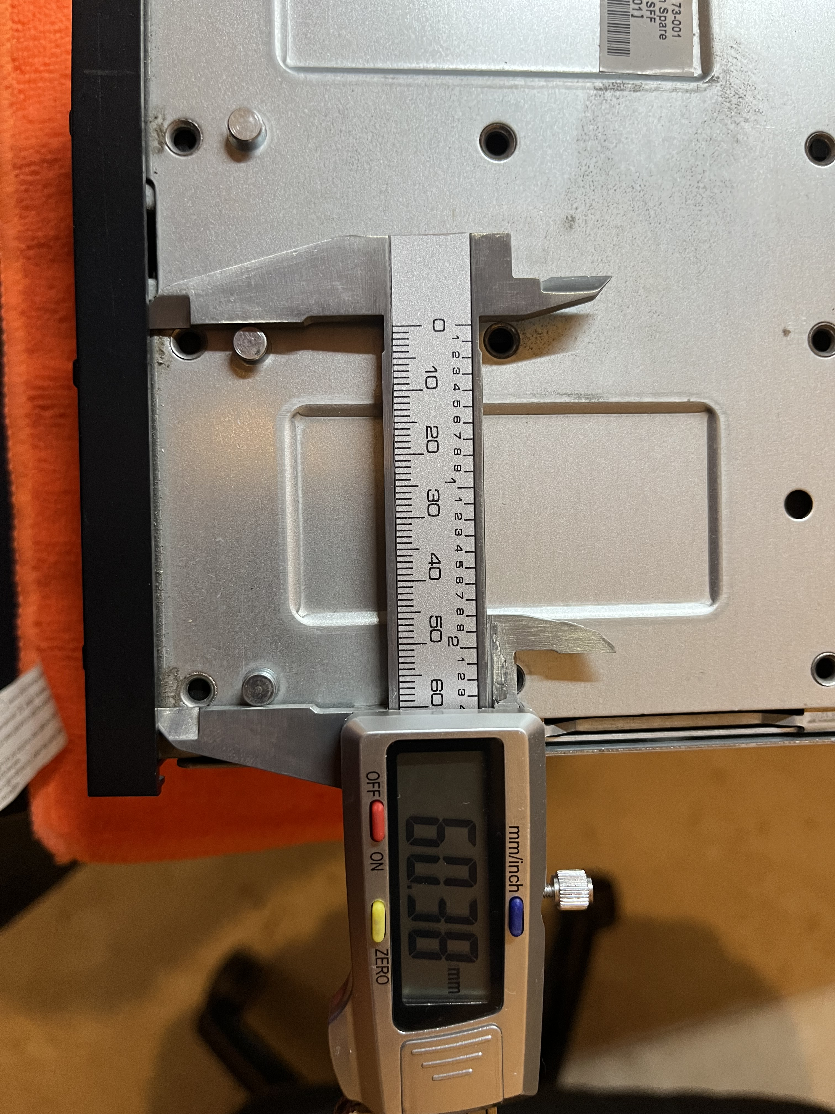
docs/digital_capler/top-mosrom-left.jpeg
