indraAsLesmana/dl380-case/docs/reference/psu-dimension/IMG_1390.jpeg

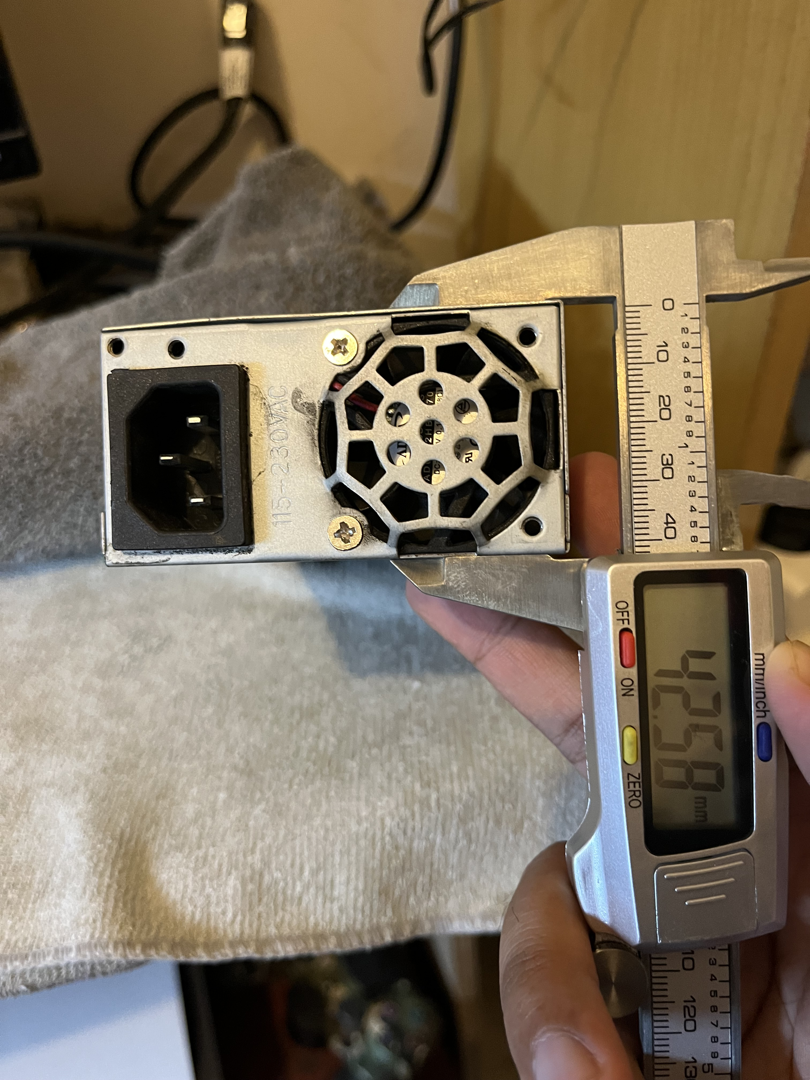
docs/reference/psu-dimension/IMG_1390.jpeg
