indraAsLesmana/dl380-case/docs/reference/psu-dimension/IMG_1391.jpeg

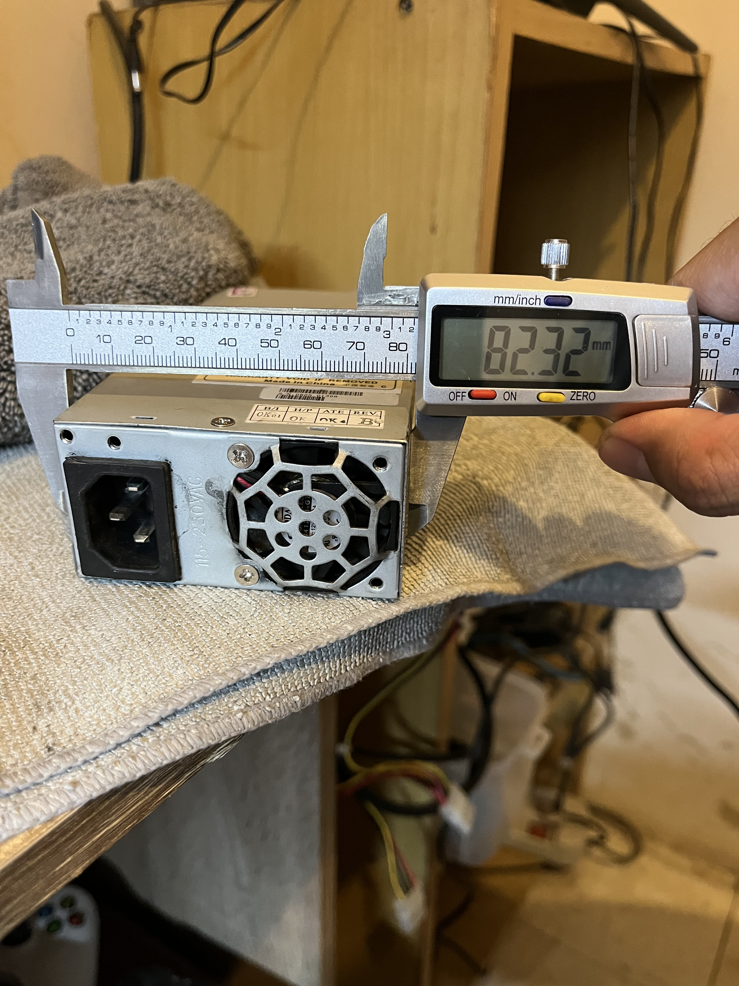
docs/reference/psu-dimension/IMG_1391.jpeg
