indraAsLesmana/dl380-case/docs/reference/psu-dimension/IMG_1392.jpeg

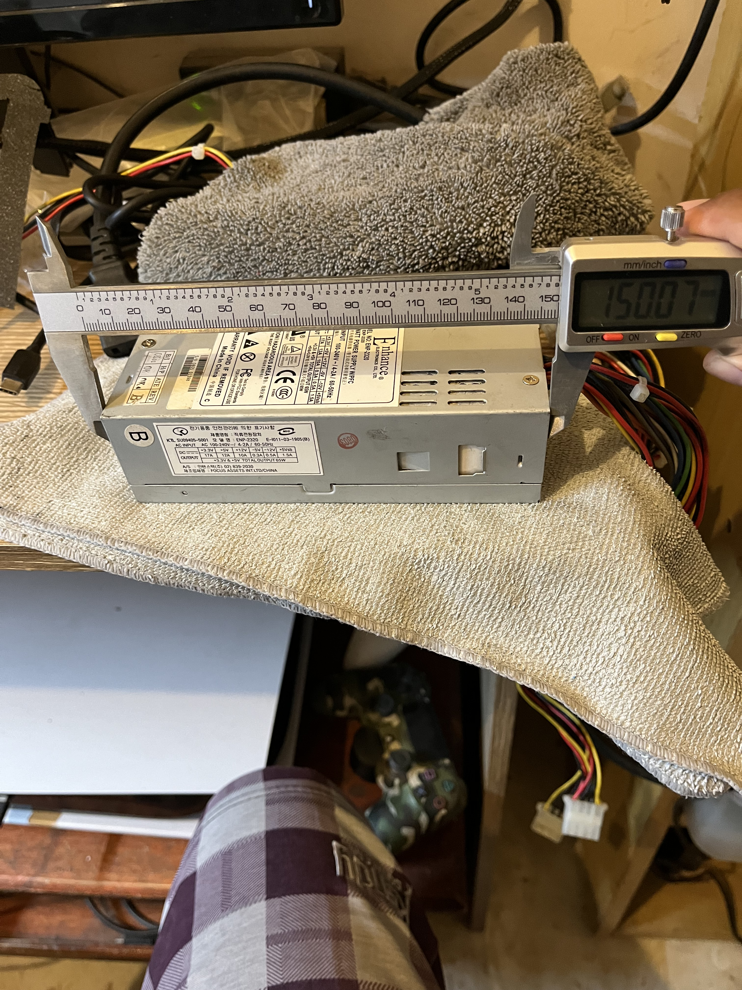
docs/reference/psu-dimension/IMG_1392.jpeg
